tomahawkmissile/LR01-Core/1.png

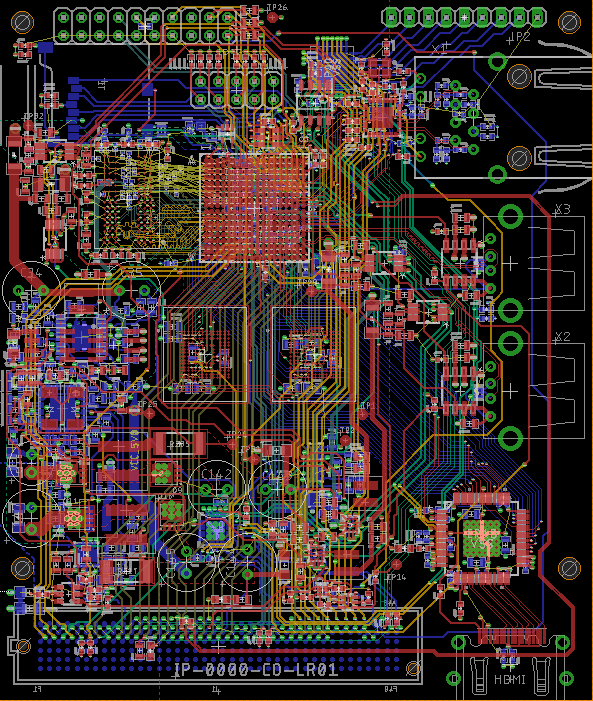
1.png
