tomahawkmissile/LR01-Core/l1.png

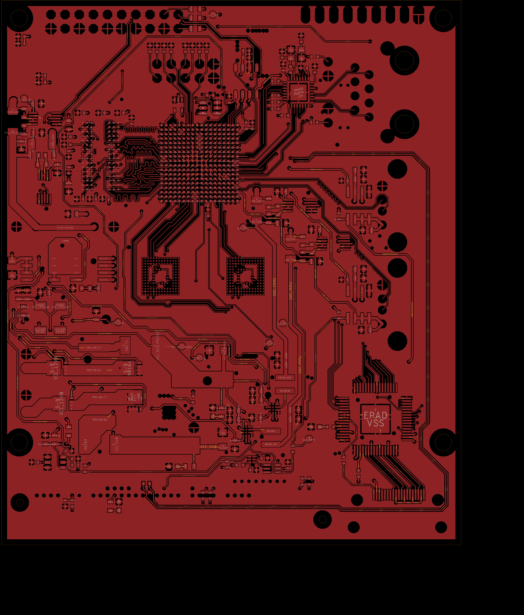
l1.png
