tomahawkmissile/LR01-Core/l2.png

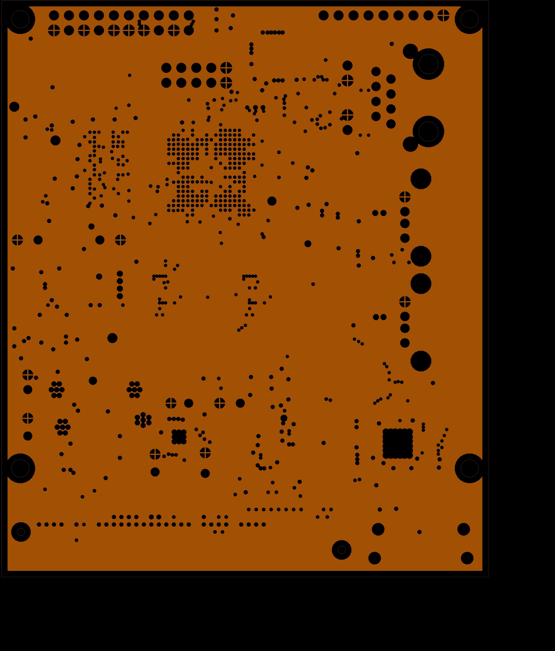
l2.png
