tomahawkmissile/LR01-Core/l4.png

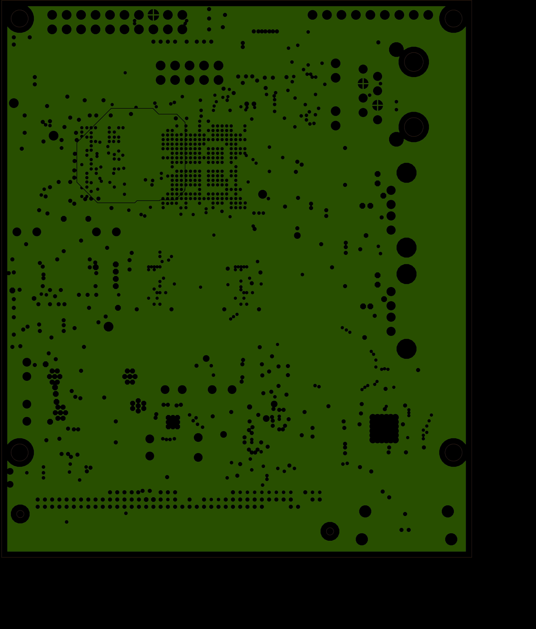
l4.png
