tomahawkmissile/LR01-Core/l5.png

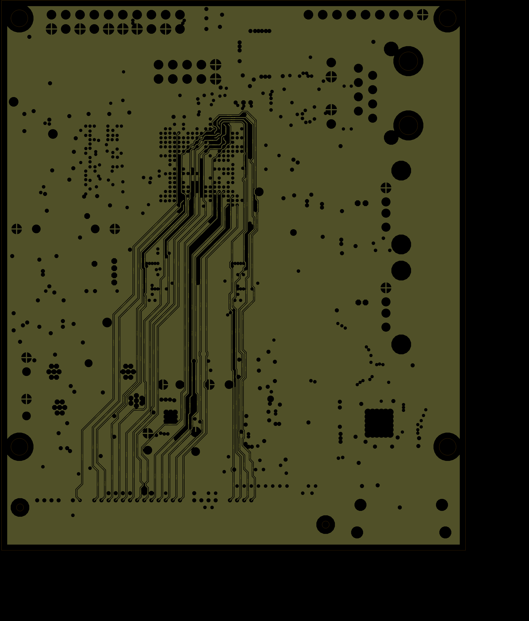
l5.png
