tomahawkmissile/LR01-Core/l16.png

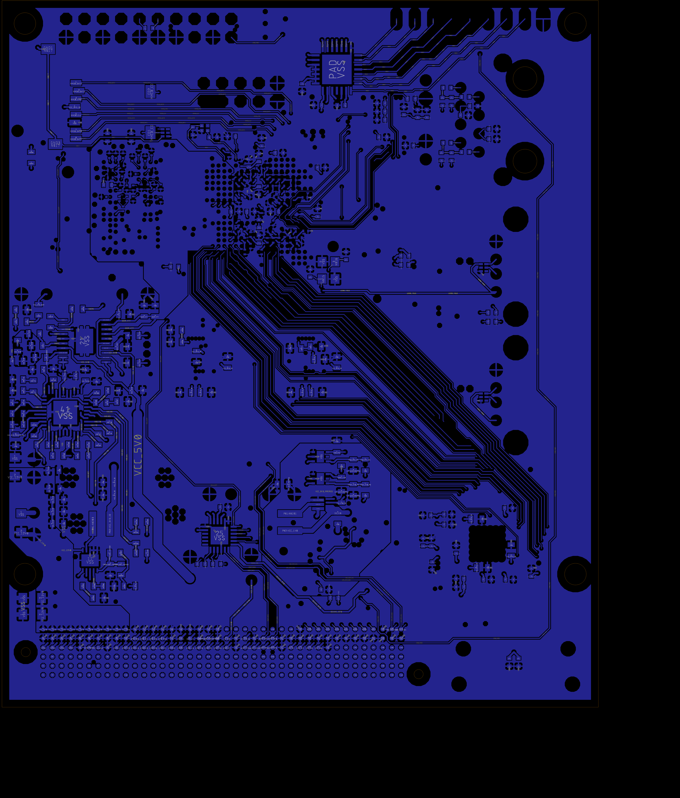
l16.png
