tomahawkmissile/LR01-Core/ldrill.png

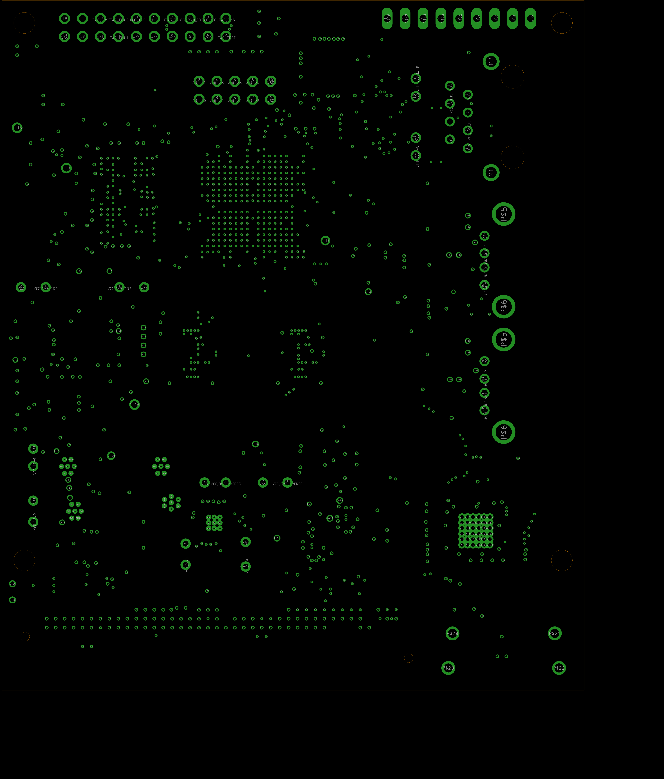
ldrill.png
